GNAT-Academic-Program/freyja/tools/qualified.py

#!/usr/bin/env python3
"""Qualified parts: the exact thing that gets soldered, and where the numbers
came from.

`ki_fp_filters` catches a footprint that disagrees with its symbol, which is
useful but weak: a filter can be absent, broad, or simply wrong, and it says
nothing about whether the part can survive the voltage on the net it is
soldered to. This file is the stronger statement -- manufacturer part number,
manufacturer package code, the footprint fitted, the ratings that matter on
*this* board, and how the pinout was confirmed.

`design.py` refuses to build if a non-generic part has no entry here, or if the
entry's footprint is not the one fitted. So a new IC cannot enter the netlist
without someone writing down what it is.

    python3 tools/qualified.py           # print the table
    python3 tools/qualified.py --write   # regenerate ref/qualified-parts.md

Lookup is by designator first, then by symbol, so parts sharing a symbol can
still carry different requirements.
"""
import sys

FP = {  # shorthand, matching design.py
    'SOT23':   'Package_TO_SOT_SMD:SOT-23',
    'SOT563':  'EasyEDA:SOT-563_L1.6-W1.2-P0.50-LS1.6-BL',
    'TSSOP8':  'EasyEDA:TSSOP-8_L4.4-W3.0-P0.65-LS6.4-BL',
    'VQFN10RPU': 'Package_DFN_QFN:Texas_RPU0010A_VQFN-HR-10_2x2mm_P0.5mm',
}

# key -> (mpn, manufacturer package, footprint, ratings that matter here,
#         how the pin map was confirmed, source of the numbers)
PARTS = {
  # ---------------------------------------------------------------- the FPGA
  'odin:XC7A100T-2FGG676I': dict(
    mpn='XC7A100T-2FGG676I', pkg='FGG676, 27x27 mm BGA, 1.0 mm pitch',
    fp='EasyEDA:FBGA-676_L27.0-W27.0-R26-C26-P1.00-BL',
    rating='VCCINT 1.0 V, VCCAUX 1.8 V, VCCO 1.8/2.5/3.3 V per HR bank',
    pinmap='all 676 balls from imported EasyEDA/LCSC C1521803 symbol; '
           'functional allocation generated by tools/alloc.py',
    src='LCSC C1521803 and AMD Artix-7 documentation'),
  # ------------------------------------------------------------- supervisor
  'MCU_RaspberryPi:RP2350B': dict(
    mpn='RP2350B', pkg='QFN-80, 10x10 mm, 0.4 mm pitch, 3.4x3.4 mm pad',
    fp='EasyEDA:QFN-80_L10.0-W10.0-P0.40-TL-EP3.4',
    rating='IOVDD 3.3 V, DVDD 1.1 V from the on-chip switcher (200 mA), '
           'ADC input 0..ADC_AVDD',
    pinmap='KiCad MCU_RaspberryPi symbol, pins resolved by name',
    src='RP2350 datasheet; RP-008280 hardware design guide'),
  'Device:Crystal_GND24': dict(
    mpn='ABM8-272-T3', pkg='3.2x2.5 mm, 4 pad',
    fp='EasyEDA:CRYSTAL-SMD_4P-L3.2-W2.5-BL',
    rating='12 MHz, +/-30 ppm, CL 10 pF, ESR 50 ohm max',
    pinmap='2-pad crystal with grounded shield; G ties both shield pads',
    src='RP-008280 s4.1 names this exact part and the 1k damping resistor'),
  'Memory_Flash:W25Q32JVZP': dict(
    mpn='W25Q32JVZPIQ', pkg='WSON-8, 6x5 mm, 1.27 mm pitch',
    fp='EasyEDA:WSON-8_L6.0-W5.0-P1.27-BL-EP',
    rating='2.7-3.6 V, 32 Mbit',
    pinmap='KiCad symbol checked against imported C571260 pads; standard QSPI NOR',
    src='Winbond W25Q32JV datasheet; LCSC C571260'),
  'odin:W25Q256JVEIQ': dict(
    mpn='W25Q256JVEIQ', pkg='WSON-8, 8x6 mm, 1.27 mm pitch',
    fp='EasyEDA:WSON-8_L8.0-W6.10-P1.27-BL-EP',
    rating='2.7-3.6 V, 256 Mbit, 25 mA program peak',
    pinmap='generated from the standard 8-pin QSPI NOR pinout, '
           'tools/gen_kicad.py FLASH_PINS',
    src='Winbond W25Q256JV datasheet; LCSC C97522'),
  'Memory_RAM:APS1604M-3SQRx-SN': dict(
    mpn='APS1604M-3SQR-SN', pkg='SOP-8 150 mil (3.9x4.9 mm)',
    fp='EasyEDA:SOIC-8_L4.9-W3.9-P1.27-LS6.0-BL',
    rating='2.7-3.6 V, 16 Mbit QSPI PSRAM, tCEM 8 us',
    pinmap='KiCad Memory_RAM symbol', src='APMemory datasheet; LCSC C18214056'),
  # ------------------------------------------------------------ power train
  'Regulator_Switching:TPS54202DDC': dict(
    mpn='TPS54202DDCR', pkg='SOT-23 (6)', fp='EasyEDA:SOT-23-6_L2.9-W1.6-P0.95-LS2.8-BL',
    rating='4.5-28 V in, 2 A out, 500 kHz, 5 ms internal soft start. '
           'The 4.5 V minimum is the binding constraint -- see findings 20',
    pinmap='KiCad Regulator_Switching symbol',
    src='TI SLVSD26C; LCSC C191884'),
  'odin:AP63300WU': dict(
    mpn='AP63300WU-7', pkg='TSOT26 (WU)', fp='EasyEDA:TSOT-23-6_L2.9-W1.6-P0.95-LS2.8-BR',
    rating='3.8-32 V input, 3 A output, 500 kHz, 0.8 V reference. '
           '3.3 V reference circuit: 93.1k/30.1k feedback, 56 pF feed-forward, '
           '4.7 uH, 10 uF input, 3x22 uF output',
    pinmap='Diodes TSOT26 top view: 1 FB, 2 EN, 3 VIN, 4 GND, 5 SW, 6 BST',
    src='Diodes Incorporated DS42002 Rev. 3-2, Table 1'),
  'Regulator_Switching:TLV62569DRL': dict(
    mpn='TLV62569DRLR', pkg='SOT-563', fp=FP['SOT563'],
    rating='2.5-5.5 V in, 2 A out, 1.5 MHz; output cap 10-47 uF',
    pinmap='KiCad Regulator_Switching symbol',
    src='TI SLVSDG1C; LCSC C163217'),
  'EasyEDA:SY8047QDC': dict(
    mpn='SY8047QDC', pkg='QFN-16-EP, 3x3 mm, 0.5 mm pitch',
    fp='EasyEDA:TQFN-16_L3.0-W3.0-P0.50-TL-EP1.6',
    rating='2.5-5.5 V in, 4 A out, 1.25 MHz, 0.6 V feedback, '
           '5 A minimum peak-current limit',
    pinmap='Imported C3018651 symbol and footprint checked against the '
           'Silergy SY8047 Rev 0.9 top-view pinout',
    src='Silergy SY8047 Rev 0.9; LCSC C3018651'),
  'Regulator_Switching:TPS61085PW': dict(
    mpn='TPS61085PWR', pkg='TSSOP-8 (PW), 3.0x4.4 mm body, 6.4 mm lead span',
    fp=FP['TSSOP8'],
    rating='2.3-6 V in, 18.5 V max out, switch limit 2.0 A min / 3.2 A max, '
           '650 kHz with FREQ grounded',
    pinmap='KiCad Regulator_Switching symbol',
    src='TI SLVS859B'),
  'odin:TPS22950CDDC': dict(
    mpn='TPS22950CDDCR', pkg='SOT-23-THIN-6 (TI DDC)', fp='EasyEDA:SOT-23-6_L2.9-W1.6-P0.95-LS2.8-BL_3',
    rating='1.8-5.5 V in, 6 V absolute max on VIN/VOUT, 3.2 A switch; '
           'adjustable current limit, thermal shutdown, fixed controlled '
           'turn-on, reverse blocking enabled and disabled. U21: 1.15k = '
           '1.000 A typical (0.75-1.25 A). U22-U24: 2.21k = 0.500 A typical '
           '(0.38-0.62 A)',
    pinmap='TI DDC top view: 1 ON, 2 VIN, 3 GND, 4 ILIM, 5 VOUT, 6 FLT',
    src='TI TPS22950x datasheet SLVSFJ2B'),
  'odin:TPS259470LRPW': dict(
    mpn='TPS259470LRPWR', pkg='VQFN-HR-10, 2x2 mm, 0.5 mm pitch (TI RPW)',
    fp=FP['VQFN10RPU'],
    rating='2.7-23 V operating, 28 V absolute max, back-to-back FETs and true '
           'reverse blocking. 6.65k ILM = 500 mA typical (425..575 mA); '
           '121k/12.1k OVLO = 13.2 V nominal; 3.3nF dVdt = about 20 ms rise; '
           'active current limiting and latch-off fault response',
    pinmap='TI RPW top view: 1 EN/UVLO, 2 OVLO, 3 AUXOFF, 4 FLT, 5 IN, '
           '6 OUT, 7 dVdt, 8 GND, 9 ILM, 10 ITIMER',
    src='TI TPS25947 datasheet SLVSFC9C'),
  'U26': dict(
    mpn='TPS259470ARPWR', pkg='VQFN-HR-10, 2x2 mm, 0.5 mm pitch (TI RPW)',
    fp=FP['VQFN10RPU'],
    rating='2.7-23 V input, true reverse blocking, auto-retry. Input path: '
           '100k/47k UVLO = 3.75 V, 73.2k/10k OVLO = 9.98 V, 1.65k ILM = '
           '2.03 A typical, 2.2 nF dVdt = 0.91 V/ms and about 40 mA into 44 uF',
    pinmap='TI RPW top view: 1 EN/UVLO, 2 OVLO, 3 AUXOFF, 4 FLT, 5 IN, '
           '6 OUT, 7 dVdt, 8 GND, 9 ILM, 10 ITIMER',
    src='TI TPS25947 datasheet SLVSFC9C'),
  'Device:D_Schottky': dict(
    mpn='SS34', pkg='SMA / DO-214AC', fp='EasyEDA:SMA_L4.3-W2.6-LS5.2-RD',
    rating='40 V, 3 A, Vf about 0.45 V at 0.5 A. D3/D4 OR the inputs, '
           'D5 rectifies the boost at 650 kHz and 2 A peak',
    pinmap='2-pin polarised', src='generic SS34, multiple vendors'),
  'Device:D_Zener': dict(
    mpn='SMBJ13A-TR', pkg='SMB / DO-214AA', fp='EasyEDA:SMB_L4.6-W3.6-LS5.3-RD',
    rating='UNIDIRECTIONAL. 13 V standoff, VBR 14.4 V min at 1 mA, '
           'VC 21.5 V at 28 A IPP, 600 W. Cathode to VBUS, anode to GND',
    pinmap='2-pin polarised; KiCad ships no unidirectional TVS symbol, so '
           'the polarised avalanche symbol stands in',
    src='Littelfuse/Diodes SMBJ series datasheet'),
  'D8': dict(
    mpn='SMBJ15A-13-F', pkg='SMB / DO-214AA', fp='Diode_SMD:D_SMB',
    rating='Unidirectional, 15 V standoff, 16.7-19.2 V breakdown, '
           '24.4 V maximum rated pulse clamp, 600 W. Transient suppression on VIN_EXT',
    pinmap='1 cathode to VIN_EXT; 2 anode to GND',
    src='Diodes SMBJ15A https://www.diodes.com/part/view/SMBJ15A; LCSC C135046'),
  'Q1': dict(
    mpn='DMG2305UX-7', pkg='SOT-23', fp='EasyEDA:SOT-23-3_L2.9-W1.3-P1.90-LS2.4-BR',
    rating='-20 V VDSS, +/-8 V VGSS, -4.2 A, RDS(on) 52 mohm max at '
           'VGS -4.5 V. Source at +3V3, so VGS never exceeds -3.3 V',
    pinmap='G-S-D SOT-23, pins 1-2-3', src='Diodes Inc DMG2305UX datasheet'),
  'Q2': dict(
    mpn='DMG2305UX-7', pkg='SOT-23', fp='EasyEDA:SOT-23-3_L2.9-W1.3-P1.90-LS2.4-BR',
    rating='-20 V VDSS, +/-8 V VGSS, -4.2 A, PD 1.4 W. 100k/47k gate divider: '
           'VGS -3.40 V at 5 V, -6.12 V at 9 V. Firmware must still forbid '
           'passing 9 V onto +5V. See findings 21',
    pinmap='G-S-D SOT-23, pins 1-2-3', src='Diodes Inc DMG2305UX datasheet'),
  'Transistor_FET:Q_NMOS_GSD': dict(
    mpn='BSS138LT1G', pkg='SOT-23', fp='EasyEDA:SOT-23-3_L2.9-W1.6-P1.90-LS2.8-BR',
    rating='50 V, 200 mA; RDS(on) max 10 ohm at VGS 2.75 V (-40..85 C). '
           'Q3 pulls a gate through 47k; Q4 sinks approximately 2-4 mA for DONE LED',
    pinmap='G-S-D SOT-23, pins 1-2-3',
    src='onsemi BSS138LT1/D, https://www.onsemi.com/pdf/datasheet/bss138lt1-d.pdf'),
  # ------------------------------------------------------------------ logic
  'odin:SN74LXC8T245PW': dict(
    mpn='SN74LXC8T245PWR', pkg='TSSOP-24 (PW)', fp='EasyEDA:TSSOP-24_L7.8-W4.4-P0.65-LS6.4-BL_1',
    rating='1.1-5.5 V on both VCCA and VCCB; VCCA=3V3, VCCB=5V here',
    pinmap='CONFIRMED against TI TSSOP-24 pinout: 1 VCCA, 2 DIR, 3-10 A1..A8, '
           '11-13 GND, 14-21 B8..B1, 22 OE, 23-24 VCCB. findings item 11',
    src='TI SCES864; symbol is AVC8T245 renamed, tools/gen_kicad.py'),
  '74xx:SN74CB3Q3384APW': dict(
    mpn='SN74CB3Q3384APWR', pkg='TSSOP-24 (PW)', fp='EasyEDA:TSSOP-24_L7.8-W4.4-P0.65-LS6.4-BL',
    rating='2.3-3.6 V VCC, 5 ohm typical channel on-resistance, 10 bits in '
           'two banks of 5. Only bank 1 is used; bank 2 OE is tied high',
    pinmap='KiCad 74xx symbol, pins resolved by name',
    src='TI SCDS131'),
  'odin:PCA9543APW': dict(
    mpn='PCA9543APW,118', pkg='TSSOP-14, SOT402-1',
    fp='Package_SO:TSSOP-14_4.4x5mm_P0.65mm',
    rating='2.3-5.5 V, 400 kHz; fitted at 3.3 V; address 0x70; POR disconnects both channels',
    pinmap='NXP Table 3: 1 A0, 2 A1, 3 RESET, 4 INT0, 5 SD0, 6 SC0, 7 VSS, '
           '8 INT1, 9 SD1, 10 SC1, 11 INT, 12 SCL, 13 SDA, 14 VDD',
    src='NXP PCA9543A_43B rev 8; LCSC C2652904'),
  'EasyEDA:PCF8574T_3,518': dict(
    mpn='PCF8574T_3,518', pkg='SOIC-16W (7.5x10.3 mm)', fp='EasyEDA:SOIC-16_L10.3-W7.5-P1.27-LS10.3-BL',
    rating='2.5-6 V, quasi-bidirectional I/O; P0-P2 sink LEDs at about 1 mA each; P3 reads core PG; P7 controls SFP power',
    pinmap='Imported EasyEDA symbol/footprint; LCSC C7605', src='NXP PCF8574 datasheet; LCSC C7605'),
  'EasyEDA:PM254-2-16-S-8.5': dict(
    mpn='PM254-2-16-S-8.5', pkg='2x16 female socket, 2.54 mm, SMT, 8.5 mm',
    fp='EasyEDA:HDR-SMD_32P-P2.54-V-F-R2-C16-LS7.1', rating='3 A per contact',
    pinmap='physical row 1..16, return row 32..17', src='HCTL drawing; LCSC C3975161'),
  'EasyEDA:ZX-PM2.54-1-16PY': dict(
    mpn='ZX-PM2.54-1-16PY', pkg='1x16 female socket, 2.54 mm, THT, 8.5 mm',
    fp='EasyEDA:HDR-TH_16P-P2.54-V-F-1', rating='3 A per contact',
    pinmap='pins 1..16 in physical order', src='Megastar drawing; LCSC C7499334'),
  'EasyEDA:PM254-2-08-S-8.5': dict(
    mpn='PM254-2-08-S-8.5', pkg='2x8 female socket, 2.54 mm, SMT, 8.5 mm',
    fp='EasyEDA:HDR-SMD_16P-P2.54-V-F-R2-C8-LS7.1', rating='3 A per contact',
    pinmap='odd/even pin pairs by physical column', src='HCTL drawing; LCSC C3975153'),
  'EasyEDA:Header-Female-2.54_1x8': dict(
    mpn='2.54-1*8P', pkg='1x8 female socket, 2.54 mm, THT',
    fp='EasyEDA:HDR-TH_8P-P2.54-V-F', rating='3 A per contact',
    pinmap='pins 1..8 in physical order', src='BOOMELE drawing; LCSC C27438'),
  'EasyEDA:PH2.54-1X1P-H25': dict(
    mpn='PH2.54-1X1P-H25', pkg='1x1 male guide post, 2.54 mm, THT',
    fp='EasyEDA:HDR-TH_1P-P2.54-V-M', rating='3 A; 6 mm mating post',
    pinmap='single grounded guide pin', src='JXTCONN drawing; LCSC C42431799'),
  'EasyEDA:Header-Male-2.54_2x3': dict(
    mpn='2.54-2*3P', pkg='2x3 male selector header, 2.54 mm, THT',
    fp='EasyEDA:HDR-TH_6P-P2.54-V-M-R2-C3-S2.54-1', rating='selector only',
    pinmap='odd/even pin pairs by physical column', src='BOOMELE drawing; LCSC C65114'),
  'EasyEDA:PZ254V-11-02P': dict(
    mpn='PZ254V-11-02P', pkg='1x2 male selector header, 2.54 mm, THT',
    fp='EasyEDA:HDR-TH_2P-P2.54-V-M', rating='selector only',
    pinmap='1 3V3, 2 external-JTAG select', src='XFCN drawing; LCSC C492401'),
  # -------------------------------------------------------- USB and the PD
  'Connector:USB_C_Receptacle_USB2.0_16P': dict(
    mpn='HC-TYPE-C-16P-01A', pkg='USB-C receptacle, 16 position, mid-mount',
    fp='Connector_USB:USB_C_Receptacle_HCTL_HC-TYPE-C-16P-01A',
    rating='5 A contacts, 20 V. Board never negotiates above 9 V',
    pinmap='KiCad Connector symbol for this exact part number',
    src='HCTL datasheet as shipped with the KiCad footprint'),
  'Interface_USB:CH224K': dict(
    mpn='CH224K', pkg='SSOP-10 with exposed pad (3.9x4.9 mm)',
    fp='EasyEDA:ESSOP-10_L4.9-W3.9-P1.0-LS6.0-TL-EP',
    rating='PD/QC sink controller, 3.3-22 V VBUS. CFG1..3 driven by the '
           'supervisor; firmware must never request above 9 V (D7)',
    pinmap='KiCad Interface_USB symbol', src='WCH CH224 datasheet'),
  'Power_Protection:ESDA6V1BC6': dict(
    mpn='ESDA6V1BC6', pkg='SOT-23-6', fp='EasyEDA:SOT-23-6_L2.9-W1.6-P0.95-LS2.8-BR',
    rating='4-line bidirectional ESD array, 6.1 V standoff. On D+, D-, '
           'CC1, CC2 -- data and CC only, never VBUS',
    pinmap='KiCad Power_Protection symbol', src='ST ESDA6V1BC6 datasheet'),
  # ------------------------------------------------------------- high speed
  'EasyEDA:DSC1123CI2-125.0000': dict(
    mpn='DSC1123CI2-125.0000', pkg='6-pad VDFN, 3.2x2.5 mm',
    fp='EasyEDA:OSC-SMD_6P-L3.2-W2.5-BL',
    rating='125 MHz LVDS, 2.25-3.63 V, +/-25 ppm, 32 mA maximum',
    pinmap='Microchip DSC1103/23 table 2-2: 1 EN, 2 NC, 3 GND, '
           '4 OUT+, 5 OUT-, 6 VDD; imported C617173 agrees',
    src='Microchip DSC1103/23 datasheet; LCSC C617173'),
  'Interface_Optical:SFP': dict(
    mpn='1888247-1', pkg='SFP/SFP+ SMT connector, 20 position',
    fp='EasyEDA:CONN-SMD_20P-P0.80-S8.20_1888247-1',
    rating='3.3 V, 1 W per module assumed', pinmap='KiCad Interface_Optical symbol',
    src='TE 1888247 drawing; LCSC C305914'),
  'odin:U77A11133001': dict(
    mpn='U77A11133001', pkg='SFP 1x1 cage, 3.2 mm solder tails',
    fp='odin:Amphenol_U77A11133001',
    rating='Manufacturer lists 2.5 Gb/s; all shield tails GND; JLC wave solder',
    pinmap='Drawing-based symbol/footprint; 20 solder tails; see ref/sfp-cage.md',
    src='Amphenol P-U77-A111X-XX0X rev H; JLC/LCSC C5355132'),
  # ------------------------------------------------------------ the rest
  'EasyEDA:F.0603.00025_P2-0603G1TS2-06T-002': dict(
    mpn='F.0603.00025/P2-0603G1TS2-06T-002', pkg='0603 (1608 metric)',
    fp='EasyEDA:LED0603-RD_GREEN', rating='green, 2.6-2.9 V, 230 mcd, 30 mA max',
    pinmap='imported C7496818: pad 1 cathode, pad 2 anode', src='LCSC C7496818'),
  'EasyEDA:HDR-IDC-2.54-2X5P': dict(
    mpn='2.54-2*5P', pkg='keyed 2x5 IDC box header, 2.54 mm, through-hole',
    fp='EasyEDA:IDC-TH_10P-P2.54_C5665', rating='1 A, keyed JTAG connection',
    pinmap='imported C5665, pins 1-10', src='LCSC C5665'),
  'EasyEDA:BM03B-SRSS-TB': dict(
    mpn='BM03B-SRSS-TB(LF)(SN)', pkg='JST-SH 3-pin vertical SMT, 1.0 mm',
    fp='EasyEDA:CONN-SMD-3P-P1.00_BM03B-SRSS-TB-LF-SN',
    rating='1 A, 50 V; keyed controller SWD connection',
    pinmap='1 SWCLK, 2 GND, 3 SWDIO; pads 4/5 mechanical', src='LCSC C160389'),
  'EasyEDA:KF301-5.0-2P': dict(
    mpn='KF301-5.0-2P', pkg='2-position 5.0 mm screw terminal, through-hole',
    fp='EasyEDA:CONN-TH_P5.00_KF301-5.0-2P',
    rating='17 A, 250 V component rating; Odin input limited to 9-14 V',
    pinmap='1 VIN_EXT (+), 2 GND (-)', src='LCSC C474881'),
  'Switch:SW_Push': dict(
    mpn='B3U-1000P', pkg='SMD tactile, 3.5x2.9 mm',
    fp='EasyEDA:KEY-SMD_B3U-1000PM', rating='32 V, 50 mA',
    pinmap='2-pin SPST', src='Omron B3U datasheet'),
}

# Connectors and keying posts: generic 2.54 mm headers, qualified as a class
# rather than one line each, because there is nothing to get wrong beyond the
# pin count and the pitch, and both are in the footprint name.
HEADER_SYMS = {
    'Connector_Generic:Conn_01x01', 'Connector_Generic:Conn_01x02',
    'Connector_Generic:Conn_01x03', 'Connector_Generic:Conn_01x16',
    'Connector_Generic:Conn_01x08',
    'Connector_Generic:Conn_02x03_Odd_Even',
    'Connector_Generic:Conn_02x05_Odd_Even',
    'Connector_Generic:Conn_02x08_Odd_Even',
    'Connector_Generic:Conn_02x16_Odd_Even',
}
GENERIC = {'Device:R', 'Device:C', 'Device:L', 'Device:Polyfuse'}


def lookup(ref, lib_id):
    return PARTS.get(ref) or PARTS.get(lib_id)


def check(parts):
    """Raise unless every non-generic part is qualified and fitted as stated."""
    bad = []
    for p in parts:
        if p['lib_id'] in GENERIC or p['lib_id'] in HEADER_SYMS:
            continue
        q = lookup(p['ref'], p['lib_id'])
        if q is None:
            bad.append(f"{p['ref']} ({p['lib_id']}) has no entry in "
                       f"tools/qualified.py")
        elif q['fp'] != p['fp']:
            bad.append(f"{p['ref']} is fitted {p['fp']!r} but qualified as "
                       f"{q['fp']!r}")
    if bad:
        raise ValueError('unqualified parts:\n  ' + '\n  '.join(bad))
    return len([p for p in parts if p['lib_id'] not in GENERIC
                and p['lib_id'] not in HEADER_SYMS])


HEAD = """# Qualified parts

**Generated by `tools/qualified.py`. Do not hand-edit.**

A footprint that matches its symbol's `ki_fp_filters` is not a qualified part.
The filter can be missing, or broad enough to admit the wrong package, and it
knows nothing about whether the part survives the voltage on the net it is
soldered to. This page is the stronger claim, and `tools/design.py` will not
build if a part here is fitted with a different footprint, or if a non-generic
part is missing from it altogether.

`NOT SELECTED` and `ASSUMED` mean exactly that. Those rows are the open work.

Ordinary passives are not listed individually. Resistors and capacitors are
0402 or 0603; what matters about them is voltage rating and dielectric, which
is [`ref/power-budget.md`](power-budget.md) and `findings.md` item 13.
Inductors *are* qualified, per rail, in
[`ref/power-budget.md`](power-budget.md) -- the requirement is computed there,
so the part is named there.

| Designator(s) | MPN | Package | Footprint | Ratings that matter here | Pin map | Source |
|---|---|---|---|---|---|---|
"""


def table(parts):
    rows, bykey = [], {}
    for p in parts:
        if p['lib_id'] in GENERIC or p['lib_id'] in HEADER_SYMS:
            continue
        key = p['ref'] if p['ref'] in PARTS else p['lib_id']
        bykey.setdefault(key, []).append(p['ref'])
    for key, refs in bykey.items():
        q = PARTS[key]
        r = ', '.join(f'`{x}`' for x in refs)
        rows.append(f"| {r} | **{q['mpn']}** | {q['pkg']} | `{q['fp']}` | "
                    f"{q['rating']} | {q['pinmap']} | {q['src']} |")
    return rows


def main():
    sys.path.insert(0, __file__.rsplit('/', 1)[0])
    from design import build
    parts = build().parts
    n = check(parts)
    rows = table(parts)
    print(f"{n} non-generic parts, all qualified, in {len(rows)} entries")
    for r in rows:
        print('  ' + r.split('|')[1].strip() + ' -> ' + r.split('|')[2].strip())
    if '--write' in sys.argv:
        open('ref/qualified-parts.md', 'w').write(HEAD + '\n'.join(rows) + '\n')
        print('wrote ref/qualified-parts.md')
    return 0


if __name__ == '__main__':
    sys.exit(main())
